RaxisInc/Legacy-Boscloner-Source/Boscloner_shield/bos_k22_shield/platform/devices/MK22F51212/startup/system_MK22F51212.h

#define SYSTEM_MK22F51212_H_
#ifdef __cplusplus
extern "C" {
#endif
#include <stdint.h>
  #define DISABLE_WDOG                 1
#define MCG_MODE_FEI                   0U
#define MCG_MODE_FBI                   1U
#define MCG_MODE_BLPI                  2U
#define MCG_MODE_FEE                   3U
#define MCG_MODE_FBE                   4U
#define MCG_MODE_BLPE                  5U
#define MCG_MODE_PBE                   6U
#define MCG_MODE_PEE                   7U
#define BOS_CLK_SETUP 					10
#define CLOCK_SETUP 		BOS_CLK_SETUP
#define CPU_XTAL_CLK_HZ                8000000u
#define CPU_XTAL32k_CLK_HZ             32768u
#define CPU_INT_SLOW_CLK_HZ            32768u
#define CPU_INT_FAST_CLK_HZ            4000000u
#define CPU_INT_IRC_CLK_HZ             48000000u
#define SYSTEM_SMC_PMPROT_VALUE        0xAAU
#if (CLOCK_SETUP == 0)
  #define DEFAULT_SYSTEM_CLOCK         20971520u
  #define MCG_MODE                     MCG_MODE_FEI
  #define SYSTEM_MCG_C1_VALUE          0x06U
  #define SYSTEM_MCG_C2_VALUE          0x24U
  #define SYSTEM_MCG_C4_VALUE          0x00U
  #define SYSTEM_MCG_SC_VALUE          0x00U
  #define SYSTEM_MCG_C5_VALUE          0x00U
  #define SYSTEM_MCG_C6_VALUE          0x00U
  #define SYSTEM_MCG_C7_VALUE          0x00U
  #define SYSTEM_OSC_CR_VALUE          0x00U
  #define SYSTEM_SMC_PMCTRL_VALUE      0x00U
  #define SYSTEM_SIM_CLKDIV1_VALUE     0x00110000U
  #define SYSTEM_SIM_SOPT1_VALUE       0x00080000U
  #define SYSTEM_SIM_SOPT2_VALUE       0x00U
#elif (CLOCK_SETUP == 1)
  #define DEFAULT_SYSTEM_CLOCK         120000000u
  #define MCG_MODE                     MCG_MODE_PEE
  #define SYSTEM_MCG_C1_VALUE          0x1AU
  #define SYSTEM_MCG_C2_VALUE          0x24U
  #define SYSTEM_MCG_C4_VALUE          0x00U
  #define SYSTEM_MCG_SC_VALUE          0x00U
  #define SYSTEM_MCG_C5_VALUE          0x01U
  #define SYSTEM_MCG_C6_VALUE          0x46U
  #define SYSTEM_MCG_C7_VALUE          0x00U
  #define SYSTEM_OSC_CR_VALUE          0x80U
  #define SYSTEM_SMC_PMCTRL_VALUE      0x60U
  #define SYSTEM_SIM_CLKDIV1_VALUE     0x01140000U
  #define SYSTEM_SIM_SOPT1_VALUE       0x00080000U
  #define SYSTEM_SIM_SOPT2_VALUE       0x00010000U
#elif (CLOCK_SETUP == 2)
  #define DEFAULT_SYSTEM_CLOCK         4000000u
  #define MCG_MODE                     MCG_MODE_BLPI
  #define SYSTEM_MCG_C1_VALUE          0x46U
  #define SYSTEM_MCG_C2_VALUE          0x27U
  #define SYSTEM_MCG_C4_VALUE          0x00U
  #define SYSTEM_MCG_SC_VALUE          0x00U
  #define SYSTEM_MCG_C5_VALUE          0x00U
  #define SYSTEM_MCG_C6_VALUE          0x00U
  #define SYSTEM_MCG_C7_VALUE          0x00U
  #define SYSTEM_OSC_CR_VALUE          0x80U
  #define SYSTEM_SMC_PMCTRL_VALUE      0x00U
  #define SYSTEM_SIM_CLKDIV1_VALUE     0x00040000U
  #define SYSTEM_SIM_SOPT1_VALUE       0x00080000U
  #define SYSTEM_SIM_SOPT2_VALUE       0x00030000U
#elif (CLOCK_SETUP == 3)
  #define DEFAULT_SYSTEM_CLOCK         4000000u
  #define MCG_MODE                     MCG_MODE_BLPE
  #define SYSTEM_MCG_C1_VALUE          0x9AU
  #define SYSTEM_MCG_C2_VALUE          0x27U
  #define SYSTEM_MCG_C4_VALUE          0x00U
  #define SYSTEM_MCG_SC_VALUE          0x02U
  #define SYSTEM_MCG_C5_VALUE          0x00U
  #define SYSTEM_MCG_C6_VALUE          0x00U
  #define SYSTEM_MCG_C7_VALUE          0x00U
  #define SYSTEM_OSC_CR_VALUE          0x00U
  #define SYSTEM_SMC_PMCTRL_VALUE      0x00U
  #define SYSTEM_SIM_CLKDIV1_VALUE     0x11170000U
  #define SYSTEM_SIM_SOPT1_VALUE       0x00080000U
  #define SYSTEM_SIM_SOPT2_VALUE       0x00030000U
#elif (CLOCK_SETUP == 4)
  #define DEFAULT_SYSTEM_CLOCK         120000000u
  #define MCG_MODE                     MCG_MODE_PEE
  #define SYSTEM_MCG_C1_VALUE          0x1AU
  #define SYSTEM_MCG_C2_VALUE          0x24U
  #define SYSTEM_MCG_C4_VALUE          0x00U
  #define SYSTEM_MCG_SC_VALUE          0x00U
  #define SYSTEM_MCG_C5_VALUE          0x01U
  #define SYSTEM_MCG_C6_VALUE          0x46U
  #define SYSTEM_MCG_C7_VALUE          0x00U
  #define SYSTEM_OSC_CR_VALUE          0x80U
  #define SYSTEM_SMC_PMCTRL_VALUE      0x60U
  #define SYSTEM_SIM_CLKDIV1_VALUE     0x01140000U
  #define SYSTEM_SIM_CLKDIV2_VALUE     0x09U
  #define SYSTEM_SIM_SOPT1_VALUE       0x00080000U
  #define SYSTEM_SIM_SOPT2_VALUE       0x00010000U
#elif (CLOCK_SETUP == 5)
  #define DEFAULT_SYSTEM_CLOCK         80000000u
  #define MCG_MODE                     MCG_MODE_PEE
  #define SYSTEM_MCG_C1_VALUE          0x1AU
  #define SYSTEM_MCG_C2_VALUE          0x24U
  #define SYSTEM_MCG_C4_VALUE          0x00U
  #define SYSTEM_MCG_SC_VALUE          0x00U
  #define SYSTEM_MCG_C5_VALUE          0x03U
  #define SYSTEM_MCG_C6_VALUE          0x50U
  #define SYSTEM_MCG_C7_VALUE          0x00U
  #define SYSTEM_OSC_CR_VALUE          0x80U
  #define SYSTEM_SMC_PMCTRL_VALUE      0x00U
  #define SYSTEM_SIM_CLKDIV1_VALUE     0x01130000U
  #define SYSTEM_SIM_SOPT1_VALUE       0x00080000U
  #define SYSTEM_SIM_SOPT2_VALUE       0x00010000U
#elif (CLOCK_SETUP == BOS_CLK_SETUP)
#define DEFAULT_SYSTEM_CLOCK         95977472U
#define MCG_MODE                     MCG_MODE_FEI
#define SYSTEM_MCG_C1_VALUE          0x06U
#define SYSTEM_MCG_C2_VALUE          0x00U
#define SYSTEM_MCG_C4_VALUE          0xE0U
#define SYSTEM_MCG_SC_VALUE          0x00U
#define SYSTEM_MCG_C5_VALUE          0x00U
#define SYSTEM_MCG_C6_VALUE          0x00U
#define SYSTEM_MCG_C7_VALUE          0x00U
#define SYSTEM_OSC_CR_VALUE          0x00U
#define SYSTEM_SMC_PMCTRL_VALUE      0x60U
#define SYSTEM_SIM_CLKDIV1_VALUE     0x01330000U
#define SYSTEM_SIM_SOPT1_VALUE       0x000C0000U
#define SYSTEM_SIM_SOPT2_VALUE       0x00U
#endif
extern uint32_t SystemCoreClock;
void SystemInit (void);
void SystemCoreClockUpdate (void);
#ifdef __cplusplus
}
#endif
